Tongtong828/OPS-MSG-Free-Seats/FreeSeats/Assets/Samples/XR Interaction Toolkit/3.2.1/AR Starter Assets/ARDemoSceneAssets/Sprites/Button - Rounded Highlight.png

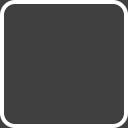
FreeSeats/Assets/Samples/XR Interaction Toolkit/3.2.1/AR Starter Assets/ARDemoSceneAssets/Sprites/Button - Rounded Highlight.png
